miketui/Combyt/agent/skills/artifact_packager.md

# Skill — Artifact Packager

Purpose:
Bundle everything a reviewer or CAD engineer needs.

Default release pack:
- STEP
- STL
- metrics JSON
- validation JSON
- report markdown
- source Python files if requested
