miketui/Combyt/docs/engineering_studies/TAYLKOMB_RevC_CAD_Handoff_Specification 2.docx

TAYLKOMB

MODULAR PROFESSIONAL COMB SYSTEM

Patent Pending — USPTO #19362254

CAD REDESIGN HANDOFF SPECIFICATION

Rev C — Drawing-Verified & Research-Backed Edition

April 12, 2026

Prepared by: Michael David Warren Jr. — TAYLKOMB LLC

Original CAD: Nathaniel Plasabas

Purpose: Finalized dimensions, materials, locking mechanism, and weight targets for CAD Rev C redesign

Drawing Source Files: Main Comb.pdf, Wide Comb.pdf, Narrow Comb.pdf, Round Comb Hande.pdf, Flat Handle.pdf, Double Handle.pdf

This document provides production-ready specifications derived from 6 original engineering drawings, cross-referenced against competitive benchmarks (Y.S. Park, Sam Villa, Hercules Sägemann), ergonomic research (CCOHS, Cal/OSHA, NIOSH), and material science data. All dimensions are in millimeters unless noted.

# 1. EXECUTIVE SUMMARY

The TAYLKOMB system consists of 6 parts: 3 comb heads (Main, Wide, Narrow) and 3 handles (Round/Rat-Tail, Flat, Double/Fork). All parts share a standardized connector interface. The Main Comb is the primary piece ("boyfriend") that accepts any of the 5 remaining parts ("girlfriend" attachments) via an integrated locking mechanism.

## Key Decisions for Rev C

1. MATERIAL: Carbon-composite heat-resistant resin for all 3 comb heads; 316L stainless steel for all 3 handles
2. LOCKING MECHANISM: Integrated dovetail rail with spring-loaded ball-detent — built into each part, zero extra assembly
3. ASSEMBLED LENGTH: Reduce from current 405–424 mm to target 280–320 mm by shortening handle working sections
4. DUAL-FAMILY STRATEGY: Narrow Comb shortened to ~198 mm for cutting/precision; Wide Comb stays at ~223 mm for detangling
5. DOUBLE HANDLE: Widen from 27.2 mm to 35 mm outer width; increase prong cross-section to 8×9 mm

# 2. CURRENT DIMENSIONS (Drawing-Verified)

All values below are extracted directly from the 6 engineering drawing PDFs created by Nathaniel Plasabas. These are the AS-DESIGNED dimensions before Rev C corrections.

## 2.1 Main Comb ("Comb Main")

Parameter | Drawing Value | Notes / Assessment
Overall length | 228.81 mm | Includes ~20.35 mm connector block. Within pro envelope (181–245 mm).
Body length (tooth span) | 208.01 mm | Standardized across all 3 combs. KEEP — matches Sam Villa Long (222 mm) range.
Secondary length | 223.81 mm | Body + partial connector measurement.
Body height | 50.75 / 50.8 mm | System datum. Consistent across all parts.
Tooth height (front view) | ~45.06 / 41.51 mm | Measured from spine to tooth region transitions. Tall for a cutting comb (typical: 25–40 mm).
Tooth thickness | 3.22 / 3.53 mm | Medium-tooth range. Acceptable.
Tooth spacing detail | 5.3 mm | Pitch dimension visible in front view.
Spine thickness | 15.86 mm (side) | Spine cross-section height from side view.
Spine/connector dims | 19.29 / 20.65 / 18.8 | Connector zone features. 18.8 mm shared across all 3 combs.
Root fillet | 0.59 mm | INCREASE to 0.8–1.0 mm — 0.59 is marginally small for breakage prevention.
Connector block (end view) | 8 × 7.73 mm features | Rail/wall elements. 5.08 mm feature thickness confirmed.
Connector protrusion | 20.35 mm | Depth of connector block from body end.

## 2.2 Wide Comb

Parameter | Drawing Value | Notes / Assessment
Overall length | 223.23 mm | KEEP — competitive with Hercules Sägemann handle combs (227 mm).
Body length | 208.01 mm | Matches Main and Narrow. System standardization confirmed.
Body height | 50.8 mm | System datum.
Tooth pitch (center-center) | 13.49 mm | VERY wide spacing — extreme wide-tooth. ~15 teeth across 208 mm body.
Tooth width | 6.19 mm | Thick teeth. Standard wide-tooth is 2–3.5 mm. Verify design intent.
Spine features | 18.95 / 20.5 / 18.8 | Spine depth and connector details. 18.8 mm shared datum.
Side profile dims | 7.86 / 2.49 / 15.64 | Tooth profile from side view. 15.64 mm = tooth depth visible in side.
Connector protrusion | 20.79 mm | Consistent with system (~20 mm).
Spine body dims | 5.47 / 4.94 / 11.52 | Internal spine section measurements.
End view cross-section | 3.31 mm | Tooth end thickness. End view shows 8 × 16 connector, 5.08 feature.

## 2.3 Narrow Comb

Parameter | Drawing Value | Notes / Assessment
Overall length | 223.67 mm | Currently matches Wide Comb. SHORTEN to ~198 mm for cutting/precision role.
Body length | 208.01 mm | System standardized. Will need shortening if adopting dual-family strategy.
Body height | 50.8 mm | System datum. Appears 3× in drawing.
Spine depth | 18.8 mm | Matches Main and Wide. System datum.
GDP tooth dimensions | 7.55 → 5.21 → 4.05 → 3.4 → 3.33 | Gradually Decreasing Pitch — EXCELLENT premium feature. Y.S. Park gold standard.
Additional tooth dims | 4.62 / 16.94 mm | Tooth section details from front view.
Spine/connector dims | 2.38 / 20.41 / 20.34 | 2.38 mm spine wall. Connector protrusions ~20 mm.
End view | 8 × 16 mm, 5.08, 2.54 | Connector cross-section. Matches system standard.

## 2.4 Round Comb Handle (Rat-Tail)

CORRECTION: Earlier audit estimated tip at 1.3 mm. Drawing confirms tip is 3.11 mm (appears 3× as 3.11, 3.1, 3.13). The 1.27 mm dimension is a connector feature, NOT the tip.

Parameter | Drawing Value | Notes / Assessment
Overall length | 242.65 mm | REDUCE to 180–200 mm to bring assembled length under 300 mm.
Working section (tail) | 187.2 mm | REDUCE to 120–140 mm. Current is 25–50% longer than typical.
Tip diameter | 3.11 mm | Adequate for plastic parting. REDUCE to 2.0–2.5 mm for precision in stainless steel.
Tail diameter (mid) | 4.8 mm (×2) | Appears twice. Good taper progression.
Connector zone | 55.6 mm | Transition from connector to tail.
Connector features | 4.95 / 2.37 / 1.27 | Internal connector dimensions. 1.27 mm is connector feature depth.
Connector block | 20.32 × 16 × 8 | 5.08 mm feature thickness. System standard.
End cross-section | 16 × 16 mm, 3.13 | Square-ish connector end. 3.13 mm internal feature.

## 2.5 Flat Handle

Parameter | Drawing Value | Notes / Assessment
Overall length | ~255.6 mm | 50.63 + 197.03 + 7.94. LONGEST PART — REDUCE to 180–200 mm.
Working section | 197.03 mm | REDUCE to 120–140 mm. Far exceeds any pro handle.
Body section | 204.95 mm | Main body before connector.
Connector end protrusion | 50.63 mm | Connector zone length.
End tip | 7.94 mm | End cap protrusion.
Cross-section (grip) | 8 × 16 mm | Very thin flat profile. 8 mm thickness, 16 mm width.
Height at transition | 7.64 mm | Transition zone height.
Edge detail | 2.55 mm | Edge radius. Adequate for comfort (R ≥ 1.5 mm target).
Connector block | 20.32 × 16 × 8 | 5.08 / 2.54 features. System standard.
Body features | 5.08 / 2.67 / 2.54 | Connector and body detail dimensions.

## 2.6 Double Handle (Fork)

Parameter | Drawing Value | Notes / Assessment
Overall length | 242.8 mm | Confirmed in 2 views. REDUCE to 180–200 mm.
Fork working length | 192 mm | REDUCE to 120–140 mm. 192 mm creates excessive flex.
Outer width | 27.2 mm | CRITICAL: WIDEN to 35 mm. Most urgent ergonomic revision.
Inner fork gap | 16.24 mm | KEEP — adequate for hair passage (≥8 mm required).
Prong cross-section | 5.43 × 5.6 mm | INCREASE to 8 × 9 mm. Current is too thin for comfort.
Body height | 50.8 mm | System datum. Confirmed.
Fork junction | 12.23 / 30.32 mm | Transition from connector to fork. 30.32 mm transition zone.
Prong wall detail | 2.5 / 2.55 mm | Wall thickness on prongs.
Connector block | 20.32 × 16 × 8 | 5.08 feature. System standard.

# 3. SHARED CONNECTOR INTERFACE (System Standard)

The following dimensions appear identically across all 6 drawings, confirming the modular connector is already designed as a shared standard. This is the foundation of the entire system and must not change without updating all 6 CAD models simultaneously.

Datum Dimension | Value | Appears In / Interpretation
Connector cross-section | 16 × 8 mm | ALL 6 parts. Primary rail/slot profile dimensions.
Feature thickness | 5.08 mm | ALL 6 parts. Rail height or retention wall.
Body height datum | 50.8 mm | Main Comb, Wide, Narrow, Double Handle. Overall mating height.
Connector block depth | 20.32 mm | Round, Flat, Double Handle. Handle-side connector protrusion.
Connector protrusion (combs) | ~20.35–20.79 mm | Main (20.35), Wide (20.79), Narrow (20.41). Comb-side.
Spine depth datum | 18.8 mm | Main, Wide, Narrow. Spine depth shared across all combs.
Feature width | 2.54 mm | Wide, Narrow, Flat, Double. Secondary feature dimension.
Body length (combs) | 208.01 mm | Main, Wide, Narrow. Standardized tooth span.

# 4. REVISED TARGET DIMENSIONS FOR REV C

These are the recommended production targets. Dimensions marked “KEEP” are drawing-verified and within competitive benchmarks. Dimensions marked “REVISE” need CAD changes before prototyping.

Part | Drawing | Rev C Target | Acceptable | Min | Max | Action
Main Comb OAL | 228.81 | 225 mm | 220–232 mm | <215 | >240 | KEEP
Main body length | 208.01 | 208 mm | 200–215 mm | <195 | >220 | KEEP
Main root fillet | 0.59 | 0.8 mm | 0.6–1.0 mm | <0.5 | N/A | REVISE
Wide Comb OAL | 223.23 | 223 mm | 218–232 mm | <210 | >240 | KEEP
Narrow Comb OAL | 223.67 | 198 mm | 190–210 mm | <185 | >215 | SHORTEN
Round Handle OAL | 242.65 | 185 mm | 175–200 mm | <170 | >210 | SHORTEN
Round tip dia. | 3.11 | 2.0 mm | 1.8–2.5 mm | <1.5 | >3.0 | REVISE
Round tail length | 187.2 | 130 mm | 120–145 mm | <110 | >160 | SHORTEN
Flat Handle OAL | ~255.6 | 190 mm | 180–205 mm | <175 | >215 | SHORTEN
Flat work section | 197.03 | 130 mm | 120–145 mm | <110 | >155 | SHORTEN
Double Handle OAL | 242.8 | 190 mm | 180–205 mm | <175 | >215 | SHORTEN
Double outer width | 27.2 | 35 mm | 32–40 mm | <30 | >45 | WIDEN
Double prong X-sec | 5.43×5.6 | 8×9 mm | 7–10 mm ea. | <6 | >13 | WIDEN
Double fork length | 192 | 130 mm | 120–145 mm | <110 | >160 | SHORTEN

ASSEMBLED LENGTH TARGETS (Rev C):

Main Comb + Round Handle: 225 + 185 − ~40 (connector overlap) = ~370 mm → Target: 280–310 mm

Main Comb + Flat Handle: 225 + 190 − ~40 = ~375 mm → Target: 280–310 mm

Main Comb + Double Handle: 225 + 190 − ~40 = ~375 mm → Target: 280–310 mm

Note: The connector engagement depth determines how much overlap reduces assembled length. A 40 mm overlap target (down from current ~50–61 mm engagement zone) is recommended to balance stability with compact length.

# 5. MATERIAL SELECTION

## 5.1 Comb Heads: Carbon-Fiber Reinforced Heat-Resistant Resin

All 3 comb heads (Main, Wide, Narrow) will use a carbon-fiber reinforced engineering polymer for heat resistance, chemical durability, and premium positioning against Y.S. Park (PEI/Ultem) and Sam Villa (silicone/graphite composite).

### Recommended: PPS-CF40 (40% Carbon-Fiber Filled Polyphenylene Sulfide)

Property | Value / Notes
Heat deflection temp (HDT) | 260–270 °C at 1.8 MPa — exceeds Y.S. Park (220 °C) and Sam Villa (232 °C)
Continuous service temp | 200–220 °C — safe for direct flat iron contact
Chemical resistance | Excellent to Barbicide, bleach, salon color developers, alcohols, peroxide
Tensile strength | 170–200 MPa — stronger than POM (61 MPa) and PEI (85 MPa)
Flexural modulus | 18,000–22,000 MPa — extremely stiff teeth with minimal flex
Water absorption | 0.02% — near-zero; dimensionally stable in wet salon
Coefficient of friction | ~0.15 (self-lubricating from carbon fiber) — smooth glide through hair
Density | 1.55–1.65 g/cm³ — light weight
Color | Natural dark gray/black — premium aesthetic. Can be custom colored.
Cost per kg | $15–30/kg — significantly less than PEI ($100–250/kg)
Moldability | Excellent flow for thin-wall injection (teeth down to 0.8 mm feasible)

Alternative option: PA66-CF30 (30% carbon-fiber filled nylon 66) at $8–15/kg. Lower heat resistance (HDT ~250 °C) but excellent mechanical properties. Downside: 1.5–2.5% water absorption may cause slight dimensional change. Best for prototyping before committing to PPS-CF40 production tooling.

## 5.2 Handles: 316L Stainless Steel

All 3 handles (Round, Flat, Double) will use 316L stainless steel for chemical resistance, durability, premium weight, and a distinctive metal-meets-carbon aesthetic.

Property | Value / Notes
Chemical resistance | Excellent — fully resistant to Barbicide, bleach, salon chemicals, acetone
Density | 8.0 g/cm³ — significantly heavier than plastic (1.4 g/cm³). Handles MUST be shortened and/or hollowed.
Tensile strength | 485–620 MPa — unbreakable in this application
Corrosion resistance | 316L has molybdenum for pitting resistance in chloride environments (bleach)
Surface finish | Brushed, polished, or bead-blasted. Recommend brushed for grip + premium look.
Manufacturing | CNC machining (prototype), MIM (production), or investment casting + machining
Cost per unit (CNC proto) | $30–80 per handle depending on complexity. MIM at volume: $8–20.
Sterilization | Autoclave-safe, immersion-safe, UV-safe. Salon-grade durability.

WEIGHT IMPACT — CRITICAL CONSIDERATION:

316L stainless at 8.0 g/cm³ is roughly 5.5× heavier than PPS-CF (1.55 g/cm³). A solid stainless handle at current dimensions would weigh 80–150 g — far too heavy. Solutions:

6. Hollow construction: Machine handles as thin-walled tubes (1.2–1.5 mm wall). Target 25–40 g per handle.
7. Shorter handles: The length reductions in Section 4 are essential — they reduce material volume by ~40%.
8. Weight budget: Comb head (PPS-CF): 12–18 g + Handle (316L hollow): 25–40 g = 37–58 g assembled. Compare to Hercules Sägemann at 30–40 g (ebonite).

## 5.3 Prototyping Material Strategy

Phase | Comb Heads | Handles | Purpose
Phase 1: Form check | FDM/SLA 3D print (ABS or Tough Resin) | FDM/SLA 3D print (ABS) | Fit, ergonomics, connector feel. 2–3 days.
Phase 2: Function proto | SLS Nylon 12 CF | CNC 316L stainless (hollow) | Real-material testing. Connector durability, weight, balance. 2–4 weeks.
Phase 3: Pre-production | Injection-molded PPS-CF40 | MIM 316L or CNC 316L | Final validation. 50–100 units. Chemical/heat testing.
Phase 4: Production | Injection-molded PPS-CF40 | MIM 316L stainless | Volume production. 1,000+ units.

# 6. LOCKING MECHANISM DESIGN

The locking mechanism connects the Main Comb ("boyfriend") to any of the 5 remaining parts ("girlfriend" attachments). The mechanism must be integrated into each part’s molded/machined geometry — no separate fasteners, springs, or assembly steps beyond sliding the pieces together.

## 6.1 Recommended: Integrated Dovetail Rail + Captive Ball-Detent

How it works: The handle slides onto the comb’s connector block along a dovetail rail. At the end of travel, a spring-loaded ball (captive inside the handle) clicks into a mating detent pocket molded into the comb body. To release, the user presses a flush thumb button on the handle that retracts the ball.

### Boyfriend Side (Main Comb / All Combs) — PPS-CF40

- 60° dovetail FEMALE rail: Molded into the connector block end of each comb body. Rail length = connector block depth (~20 mm). Rail cross-section: 8 × 5.08 mm profile with 60° angled walls.
- Detent pocket: 90° conical pocket molded into the dovetail rail surface at the end-of-travel position. Pocket diameter: 3.5 mm. Pocket depth: 0.8 mm. PPS-CF is hard enough to serve as the detent surface without a metal insert.
- Hard stop shoulder: A molded shoulder at the end of the rail that prevents over-insertion. The handle slides in until it bottoms against this shoulder — click.
- Lead-in chamfer: 30° chamfer × 1.0 mm at the rail entry. Guides insertion and sheds hair/debris.

### Girlfriend Side (All Handles) — 316L Stainless

- 60° dovetail MALE rail: Machined/MIM’d into the connector end of each handle. Mates with the comb’s female rail. Clearance: 0.10–0.15 mm per side for smooth sliding without wobble.
- Captive ball plunger: A 3 mm 316L stainless ball + 302 stainless compression spring installed in a cross-drilled bore in the handle’s connector block. Ball protrudes 0.8 mm above rail surface when engaged. Spring force: 8–12 N. This is a standard commercial component (e.g., Carr Lane CL-10-BPN or equivalent) press-fit during handle manufacture.
- Thumb release button: A flush button machined into the handle body directly above the ball plunger. Pressing it depresses the ball below the rail surface, allowing the handle to slide off. Button protrusion: 0.3 mm above handle surface (tactile but snag-free).
- Hair-shed chamfer: 0.5 mm × 45° chamfer around the entire connector seam perimeter. Prevents hair from catching at the comb-handle junction.

## 6.2 Specification Table

Parameter | Target Value | Notes
Dovetail angle | 60° included | Industry standard for small profiles. Equal play distribution.
Rail engagement length | 18–22 mm | Within the ~20 mm connector block depth. Wobble-free.
Rail clearance (per side) | 0.10–0.15 mm | Smooth slide without rattle. Achievable in CNC 316L.
Ball plunger diameter | 3 mm | Standard size. 316L ball for corrosion resistance.
Detent engagement force | 8–12 N | Comfortable hand press. Audible/tactile click.
Detent pocket diameter | 3.5 mm | 90° conical. Molded into PPS-CF comb body.
Detent pocket depth | 0.8 mm | Secure lock without requiring excessive release force.
Seam step (max) | ≤0.15 mm | Flush junction. No lip for hair to catch.
Lead-in chamfer | 30° × 1.0 mm | Both sides. Hair-shedding + easy insertion.
Cycle life target | 15,000+ swaps | Steel ball on PPS-CF detent. PPS wear is excellent.
Anti-rotation | Dovetail geometry | 60° dovetail inherently prevents rotation. No key needed.
Release method | Thumb button | Flush-mounted. Depresses ball to allow slide-off.
Assembly at manufacture | Ball plunger press-fit | Single press-fit operation during handle production. No glue.

## 6.3 Alternative Locking Concepts (For Discussion)

9. Magnetic assist + mechanical lock: N52 neodymium magnets embedded in both parts provide initial alignment/attraction, with the dovetail rail providing structural connection. Pro: satisfying magnetic snap feel. Con: magnets add cost ($0.50–1.50 per magnet), attract metal debris, and can interfere with salon tools.
10. Bayonet twist-lock: Quarter-turn bayonet with spring detent. Pro: extremely strong lock, proven in medical instruments. Con: slower swap (requires alignment + twist), can trap hair in rotational channel.
11. Collet clamp: A split-collet collar on the handle that tightens around a cylindrical post on the comb. Pro: zero wobble, adjustable tension. Con: requires a turning ring, adds complexity, slower swap.

# 7. WEIGHT BUDGET

Part | Material | Target (g) | Max (g) | Notes
Main Comb | PPS-CF40 | 14–18 | 22 | Lightweight carbon composite
Wide Comb | PPS-CF40 | 16–20 | 25 | Slightly heavier (more teeth)
Narrow Comb | PPS-CF40 | 10–14 | 18 | Shorter body (198 mm)
Round Handle | 316L SS hollow | 25–35 | 42 | 1.2 mm wall tube
Flat Handle | 316L SS hollow | 28–38 | 45 | Flat profile, wider cross-section
Double Handle | 316L SS hollow | 30–40 | 48 | Two prongs, wider overall

ASSEMBLED WEIGHT TARGETS:

Comb + Handle (any combo): 40–58 g target, 70 g maximum

Reference: Hercules Sägemann handle comb = 30–40 g (all-ebonite). Mason Pearson C2 = ~45 g (cellulose acetate).

The steel handles will give TAYLKOMB a noticeably heavier, more premium feel than all-plastic competitors. This is a positioning advantage ("substantial, professional instrument") as long as assembled weight stays under 70 g.

# 8. CAD REVISION PRIORITY (Rev C Checklist)

# | Revision | Part(s) | Urgency

1 | Design dovetail rail + ball-detent locking mechanism into connector block | ALL 6 parts | IMMEDIATE
2 | Shorten all 3 handles to 180–200 mm OAL; reduce working sections to 120–140 mm | Round, Flat, Double | IMMEDIATE
3 | Widen Double Handle to 35 mm outer; increase prong cross-section to 8×9 mm | Double Handle | IMMEDIATE
4 | Shorten Narrow Comb to ~198 mm OAL (dual-family cutting/precision role) | Narrow Comb | IMMEDIATE
5 | Convert handle geometry to hollow-wall stainless steel (1.2–1.5 mm wall) | Round, Flat, Double | NEXT PASS
6 | Slim Round Handle tip from 3.11 mm to 2.0 mm for precision parting | Round Handle | NEXT PASS
7 | Increase Main Comb root fillet from 0.59 mm to 0.8 mm | Main Comb | NEXT PASS
8 | Add hair-shed chamfers (0.5 mm × 45°) at all connector seam edges | ALL 6 parts | NEXT PASS
9 | Add thumb-release button geometry to all 3 handles | Round, Flat, Double | NEXT PASS
10 | Add brushed texture zones to handle grip areas (knurling or micro-groove) | Round, Flat, Double | PRE-PROTOTYPE

# 9. COMPETITIVE POSITIONING SUMMARY

TAYLKOMB occupies a genuinely uncontested market position. No modular comb system exists in the professional beauty industry.

Competitor | Length | Weight | Material | Heat Rating | Modular?
Y.S. Park 339 | 181 mm | ~9 g | PEI/Ultem | 220 °C | NO
Sam Villa Long | 222 mm | 20 g | Carbon/graphite | 232 °C | NO
Hercules Sägemann | 203–230 mm | 30–40 g | Ebonite | Heat resistant | NO
Mason Pearson C2 | 197 mm | ~45 g | Cellulose acetate | Low | NO
TAYLKOMB (Rev C) | 198–225 mm | 40–58 g | PPS-CF + 316L SS | 260 °C+ | YES — ONLY

TAYLKOMB’s combination of PPS-CF40 carbon composite combs (260 °C HDT) with 316L stainless steel handles creates a premium material story that exceeds every competitor on heat resistance, chemical durability, and build quality — while being the only modular system on the market.

END OF SPECIFICATION — TAYLKOMB Rev C CAD Handoff

CONFIDENTIAL — TAYLKOMB LLC — Michael David Warren Jr.

CONFIDENTIAL — TAYLKOMB LLC — Page

TAYLKOMB MODULAR COMB SYSTEM | CAD HANDOFF SPECIFICATION | REV C | APRIL 2026
