miketui/Combyt/reference/original_cad/stl/Double Handle.stl

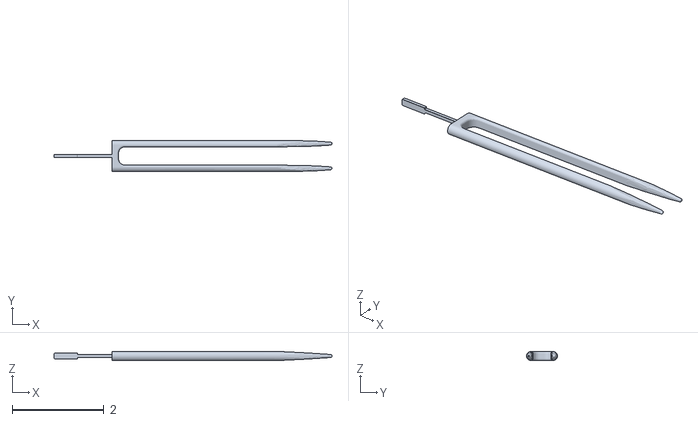
[picture p15: CAD file, 2026-04-16]
reference/original_cad/stl/Double Handle.stl
6.07 x 0.68 x 0.2
