miketui/Combyt/output/sweep_a/step/flat_handle_A_flat_01.step

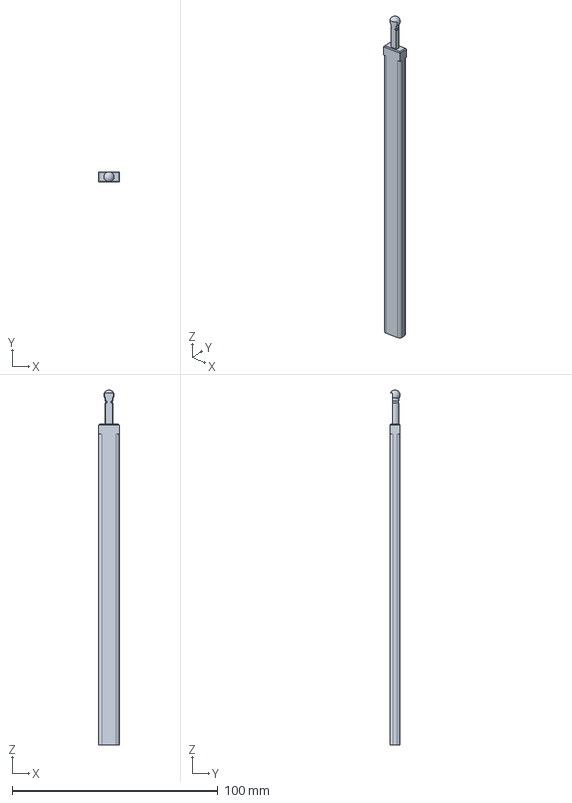
[picture p16: CAD file, 2026-04-16]
output/sweep_a/step/flat_handle_A_flat_01.step
10.0 x 5.00 x 172.5 mm
