miketui/Combyt/reference/original_cad/step/TC-002_Narrow_Comb.step

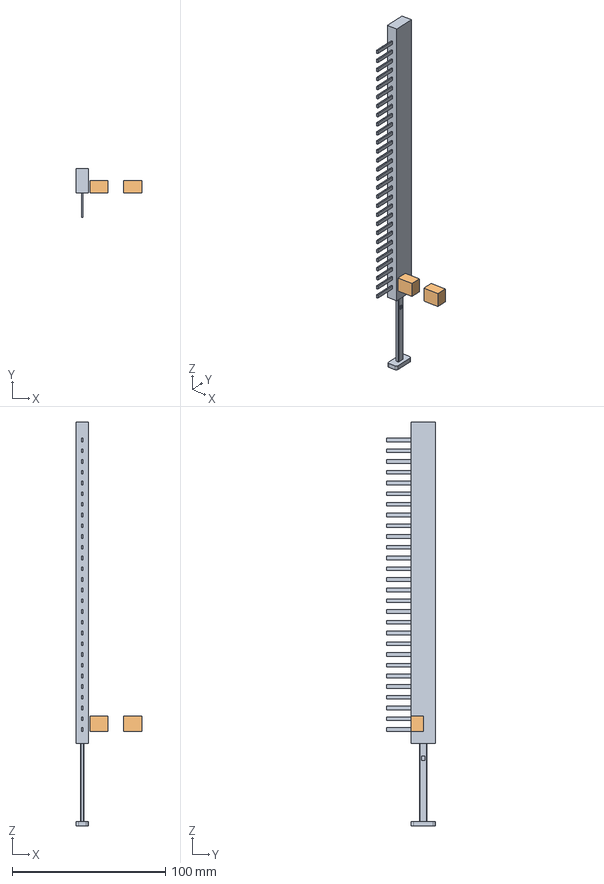
[picture p17: CAD file, 2026-04-16]
reference/original_cad/step/TC-002_Narrow_Comb.step
43.0 x 32.0 x 263.8 mm
