miketui/Combyt/output/sweep_a/step/wide_comb_A_wide_01.step

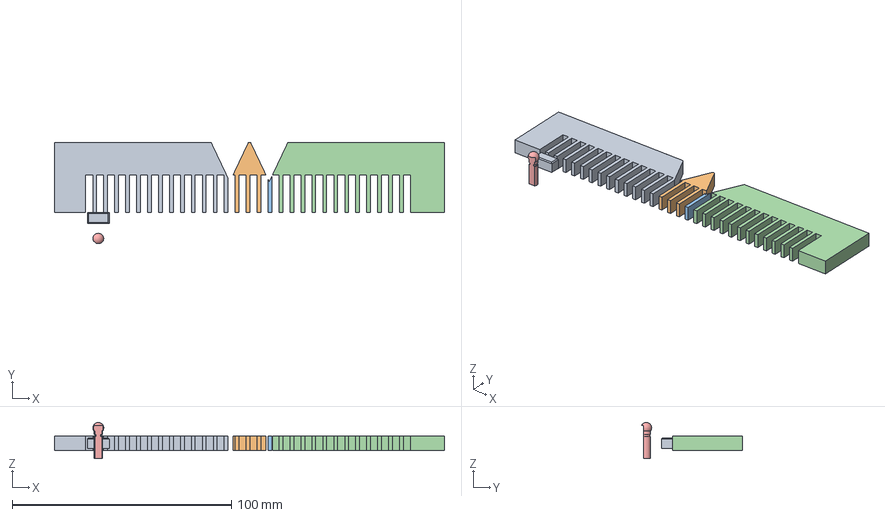
[picture p18: CAD file, 2026-04-16]
output/sweep_a/step/wide_comb_A_wide_01.step
178.0 x 46.3 x 16.5 mm
