miketui/Combyt/reference/original_cad/step/TH-003_Round_Handle.step

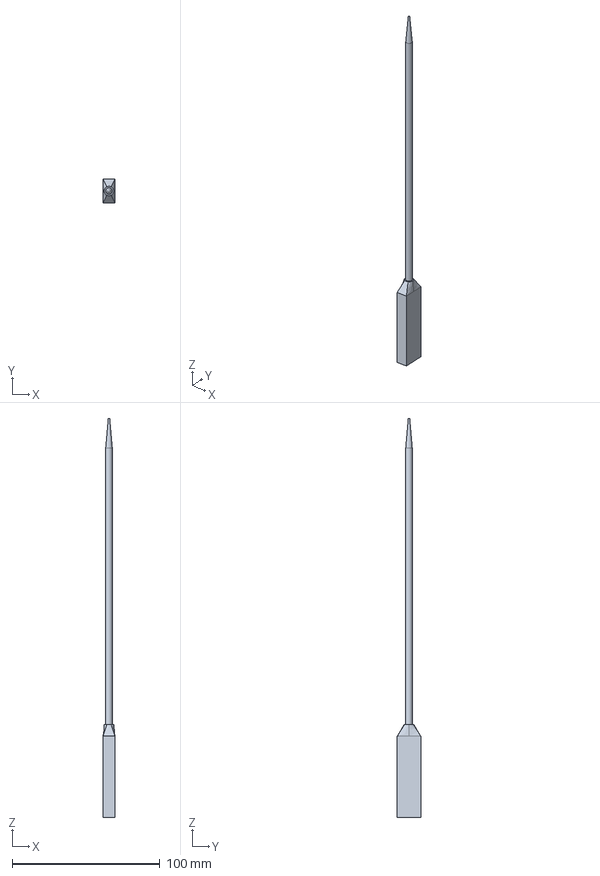
[picture p19: CAD file, 2026-04-16]
reference/original_cad/step/TH-003_Round_Handle.step
8.00 x 16.0 x 270.0 mm
